ubermajestix/16Bars/Panel/Footprints/.svg2shenzhen-cache/images/F.Cu_g186.png

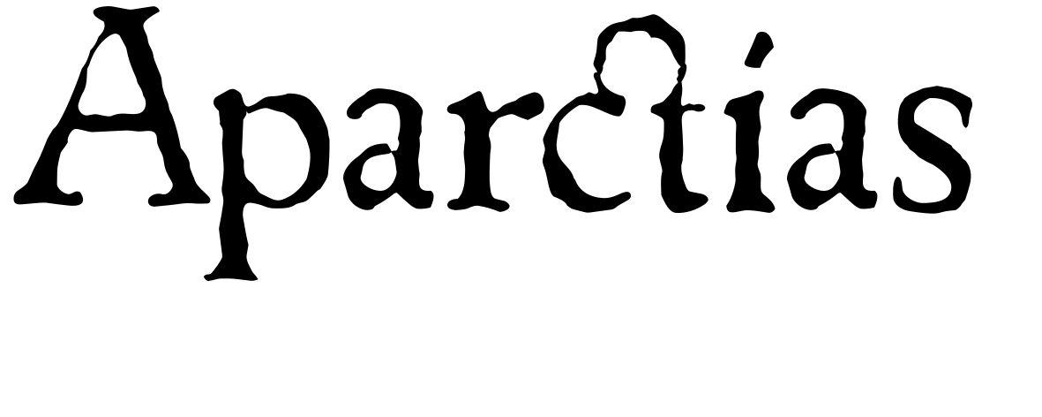
Panel/Footprints/.svg2shenzhen-cache/images/F.Cu_g186.png
