ubermajestix/16Bars/Panel/Footprints/.svg2shenzhen-cache/images/F.Cu_g1904.png

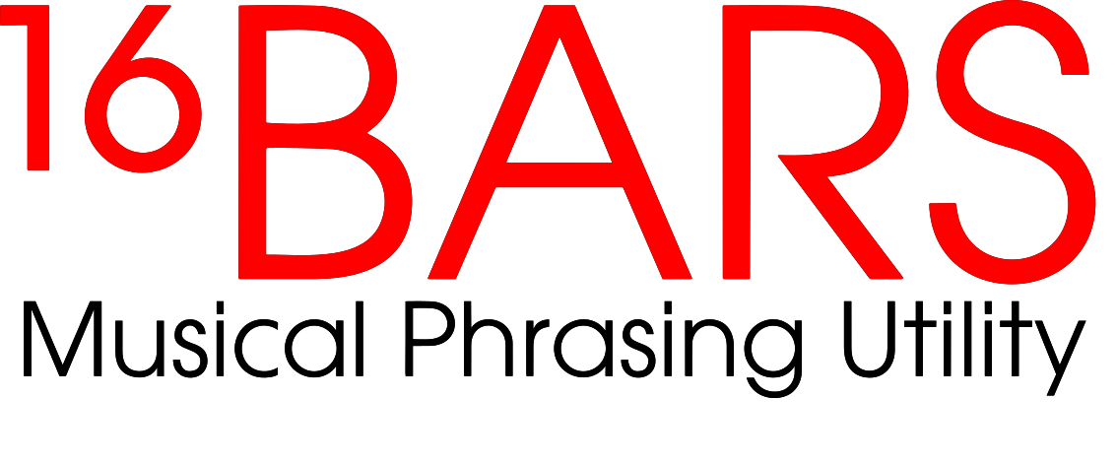
Panel/Footprints/.svg2shenzhen-cache/images/F.Cu_g1904.png
